JaredC01/LabStack/LabStack Modules/STLs/Module Radxa X4 with Heatsink/Module 1x Radxa X4 with Heatsink.stl

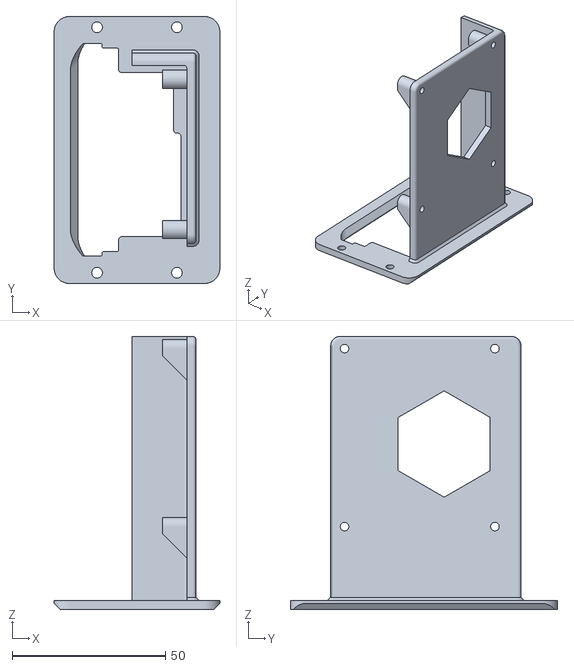
[picture p18: CAD file, 2025-01-17]
LabStack Modules/STLs/Module Radxa X4 with Heatsink/Module 1x Radxa X4 with Heatsink.stl
54.0 x 87.0 x 89.0
