JaredC01/LabStack/LabStack Mini/Accessories/STLs/M4 Mac Mini Spacer x2.stl

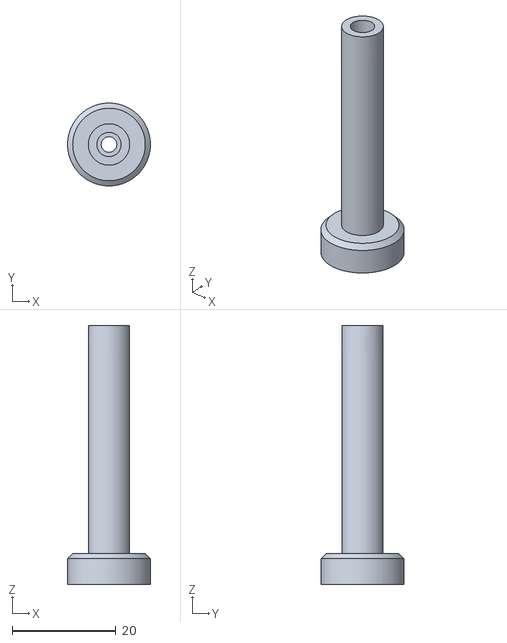
[picture p19: CAD file, 2025-01-20]
LabStack Mini/Accessories/STLs/M4 Mac Mini Spacer x2.stl
16.0 x 16.0 x 50.0
