JaredC01/LabStack/LabStack Modules/STLs/Module 2x Pi with Fan/Module 2x Pi with Fan.stl

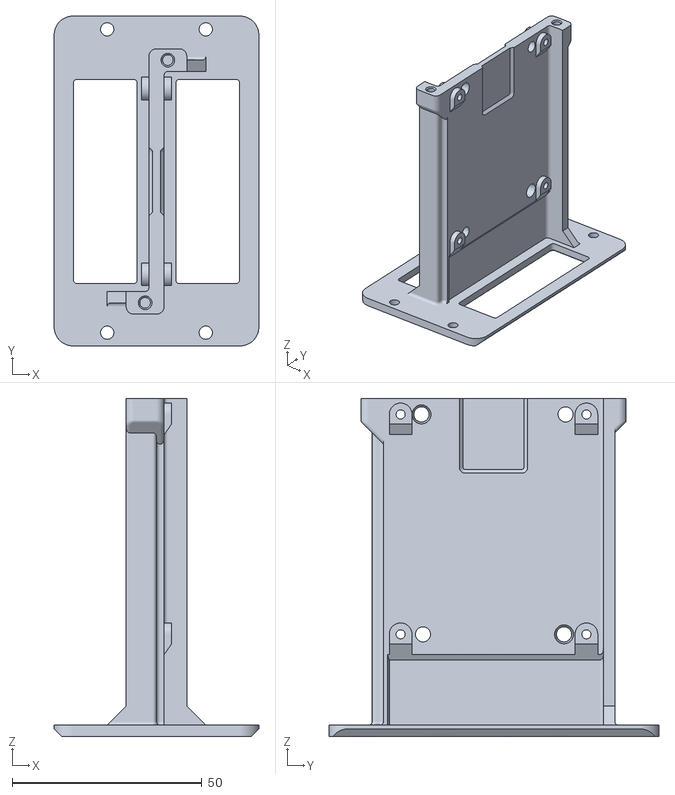
[picture p20: CAD file, 2025-08-05]
LabStack Modules/STLs/Module 2x Pi with Fan/Module 2x Pi with Fan.stl
54.0 x 87.0 x 89.1
