JaredC01/LabStack/LabStack Modules/STLs/Module 3x 25 SSD.stl

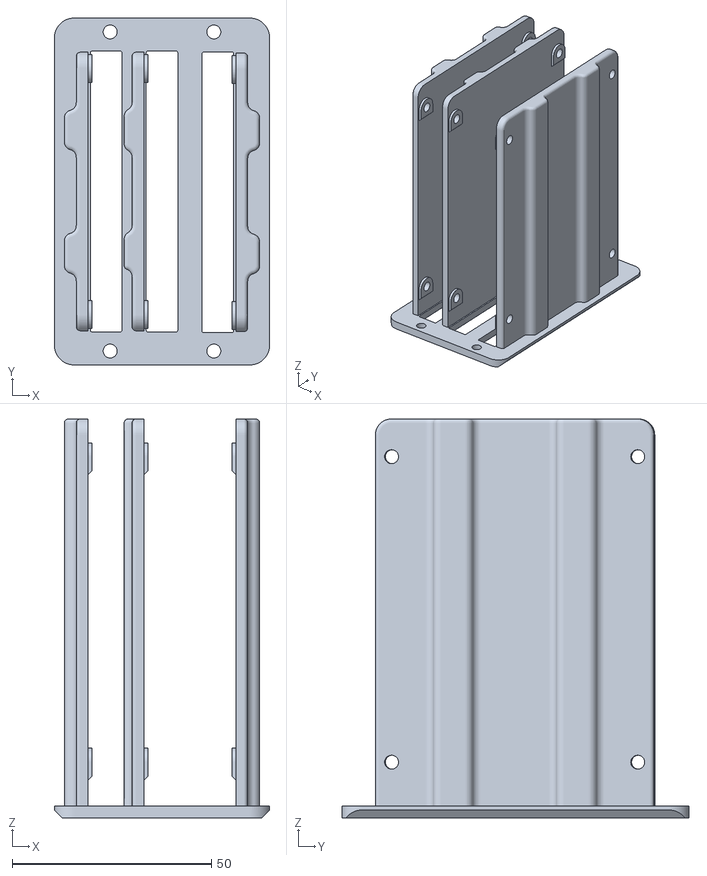
[picture p21: CAD file, 2025-02-13]
LabStack Modules/STLs/Module 3x 25 SSD.stl
54.0 x 87.0 x 100.0
