JaredC01/LabStack/LabStack Mini/Accessories/STLs/Split Bracket Brace x2.stl

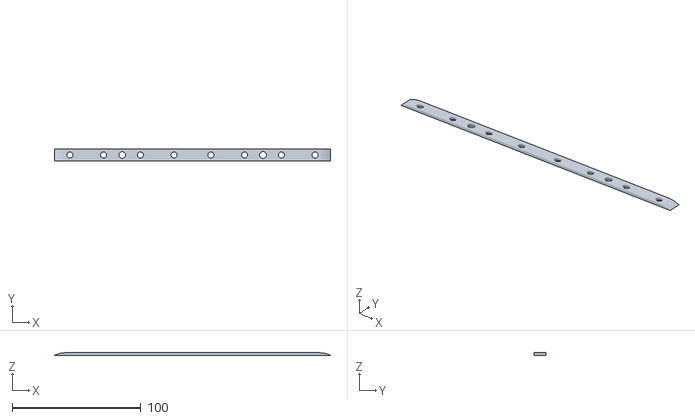
[picture p22: CAD file, 2025-01-18]
LabStack Mini/Accessories/STLs/Split Bracket Brace x2.stl
214.0 x 9.00 x 2.00
