JaredC01/LabStack/LabStack Modules/STLs/Module 1x Pi with 25 SSD.stl

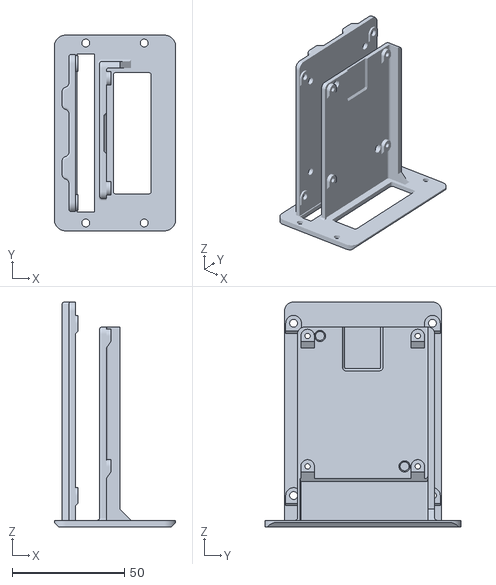
[picture p23: CAD file, 2025-02-13]
LabStack Modules/STLs/Module 1x Pi with 25 SSD.stl
54.0 x 87.0 x 100.0
