JaredC01/LabStack/LabStack Mini/Accessories/STLs/1U Mini 2x Keystone 2x SMA Left Mount.stl

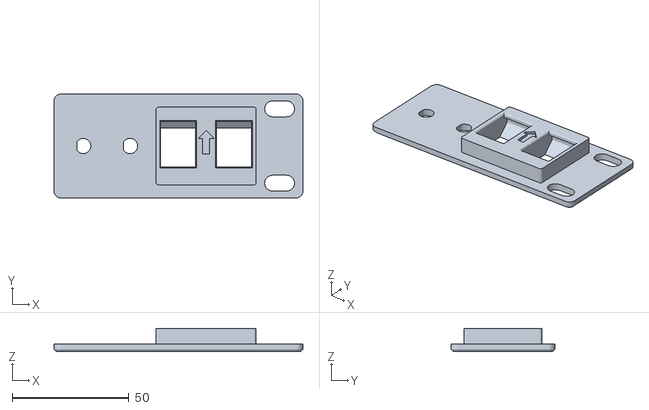
[picture p24: CAD file, 2025-01-17]
LabStack Mini/Accessories/STLs/1U Mini 2x Keystone 2x SMA Left Mount.stl
106.4 x 44.4 x 10.0
