JaredC01/LabStack/LabStack Modules/STLs/Module 2x 25 SSD.stl

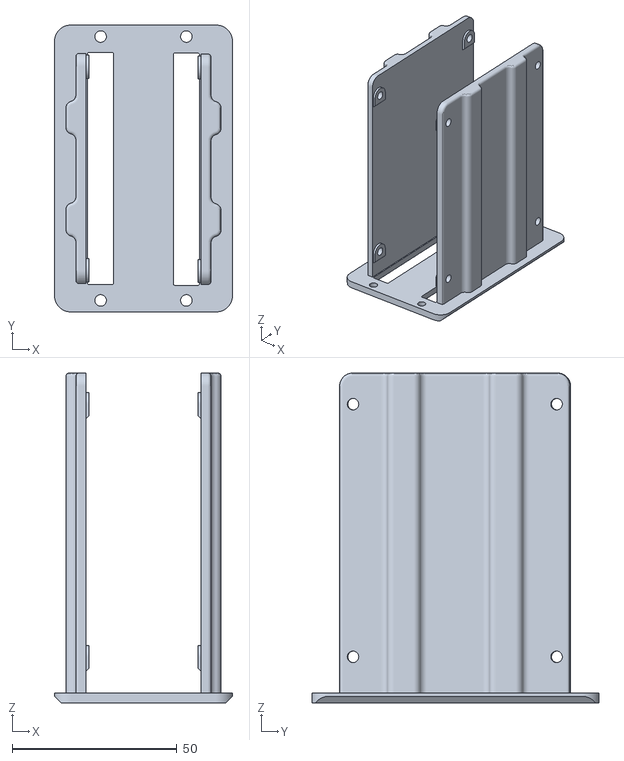
[picture p25: CAD file, 2025-02-12]
LabStack Modules/STLs/Module 2x 25 SSD.stl
54.0 x 87.0 x 100.0
