JaredC01/LabStack/LabStack Mini/Accessories/STLs/1U Mini 2x Keystone Right Mount.stl

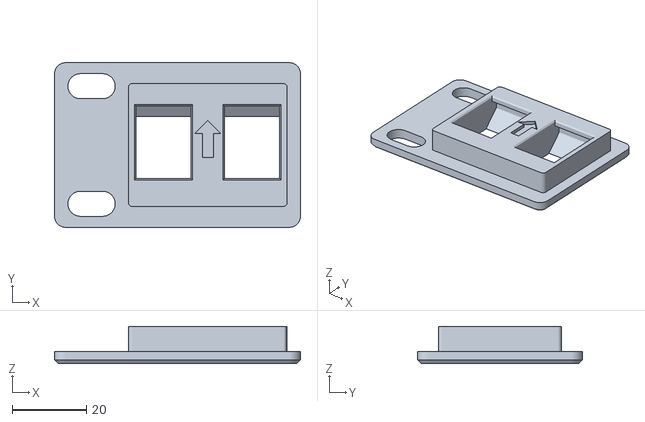
[picture p26: CAD file, 2025-01-17]
LabStack Mini/Accessories/STLs/1U Mini 2x Keystone Right Mount.stl
66.4 x 44.5 x 10.0
