JaredC01/LabStack/LabStack Modules/STLs/Module 1x JetKVM with Logo.stl

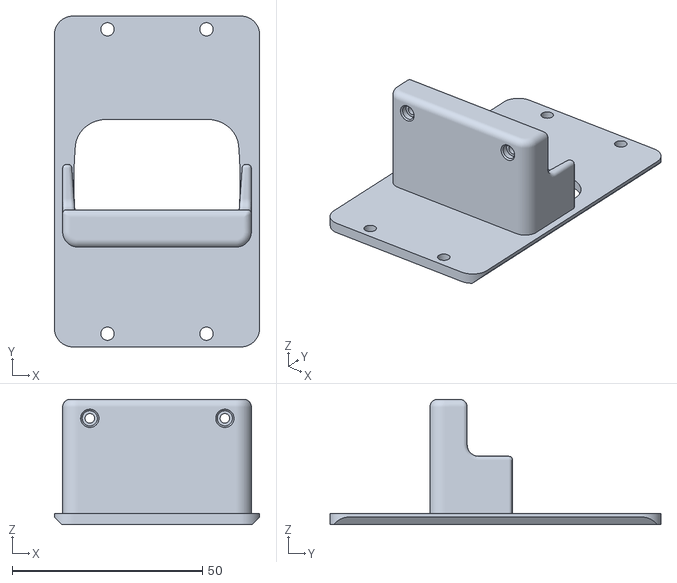
[picture p27: CAD file, 2025-02-12]
LabStack Modules/STLs/Module 1x JetKVM with Logo.stl
54.0 x 87.0 x 33.0
