JaredC01/LabStack/LabStack Modules/STLs/Module WaveShare 2.8in DSI Display.stl

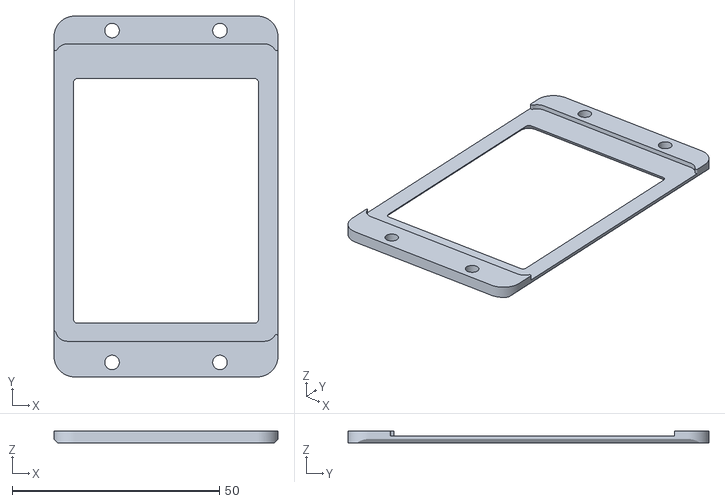
[picture p28: CAD file, 2025-01-31]
LabStack Modules/STLs/Module WaveShare 2.8in DSI Display.stl
54.0 x 87.0 x 3.00
