JaredC01/LabStack/LabStack Mini/Accessories/STLs/1U Mini Blank Panel.stl

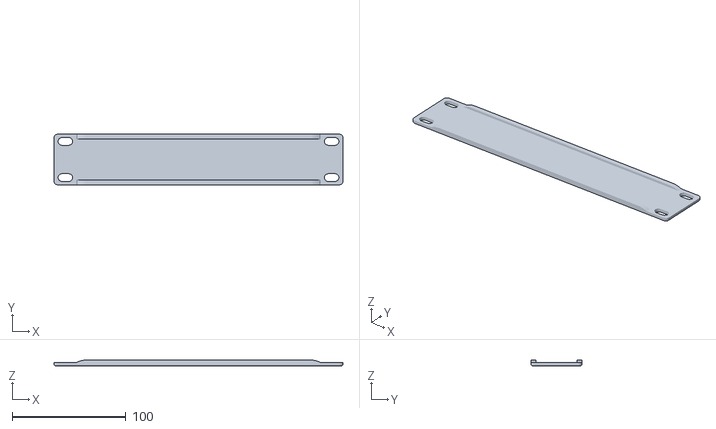
[picture p29: CAD file, 2025-01-17]
LabStack Mini/Accessories/STLs/1U Mini Blank Panel.stl
254.0 x 44.4 x 5.20
