JaredC01/LabStack/LabStack Mini/Accessories/STLs/2U Mini 2x 80mm Fan Panel.stl

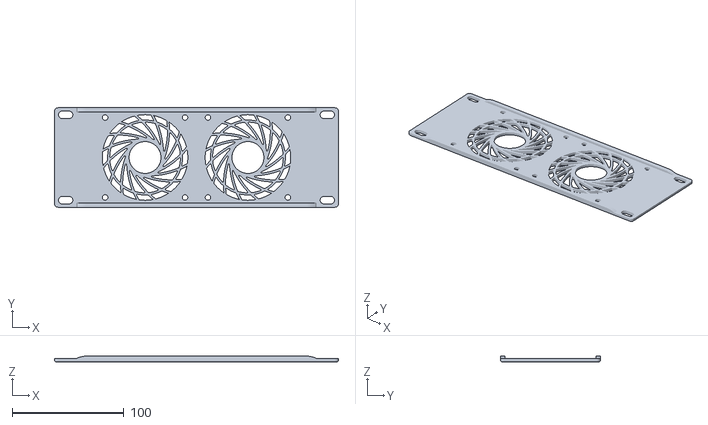
[picture p30: CAD file, 2025-01-17]
LabStack Mini/Accessories/STLs/2U Mini 2x 80mm Fan Panel.stl
254.0 x 89.0 x 5.20
