JaredC01/LabStack/LabStack Modules/STLs/Module 1x JetKVM 2x Keystone.stl

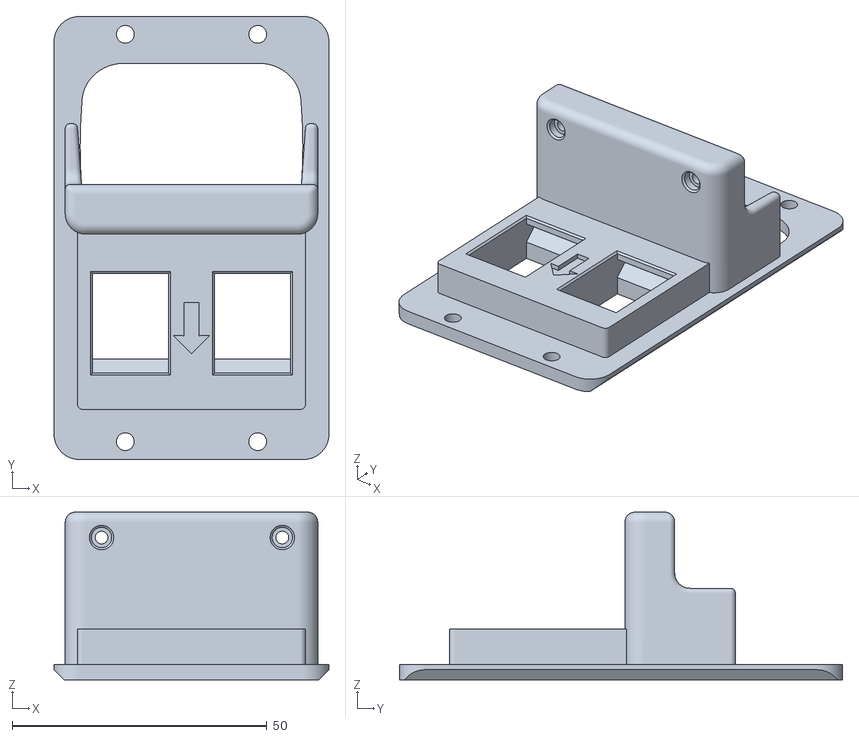
[picture p31: CAD file, 2025-01-20]
LabStack Modules/STLs/Module 1x JetKVM 2x Keystone.stl
54.0 x 87.0 x 33.0
