JaredC01/LabStack/LabStack Modules/STLs/Module 2x Keystone with Passthru.stl

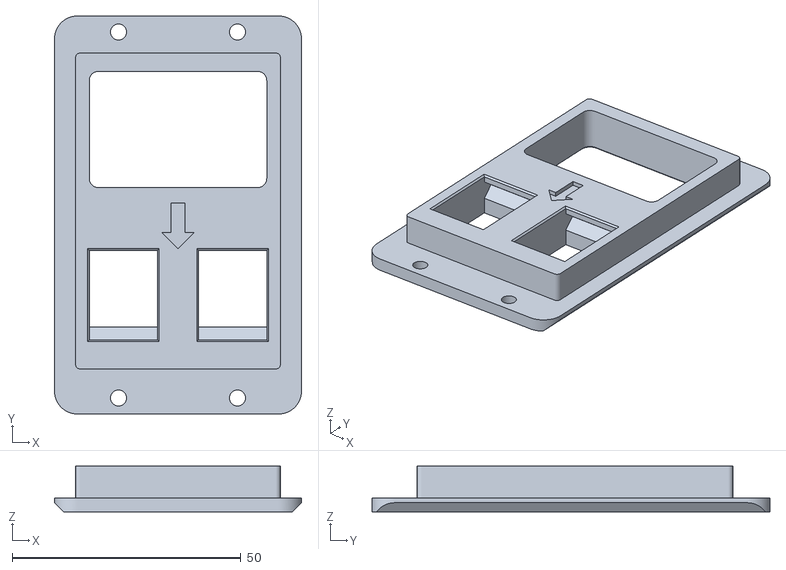
[picture p32: CAD file, 2025-01-17]
LabStack Modules/STLs/Module 2x Keystone with Passthru.stl
54.0 x 87.0 x 10.00
