JaredC01/LabStack/LabStack Modules/STLs/Module 4x Keystone.stl

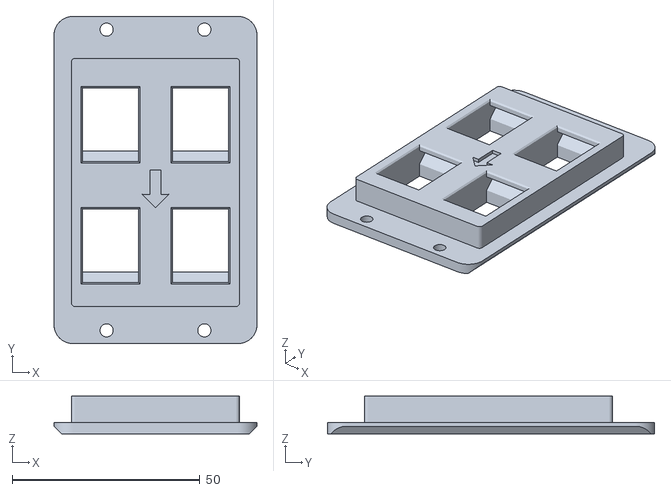
[picture p33: CAD file, 2025-01-17]
LabStack Modules/STLs/Module 4x Keystone.stl
54.0 x 87.0 x 10.0
