JaredC01/LabStack/LabStack Modules/STLs/Module Blank.stl

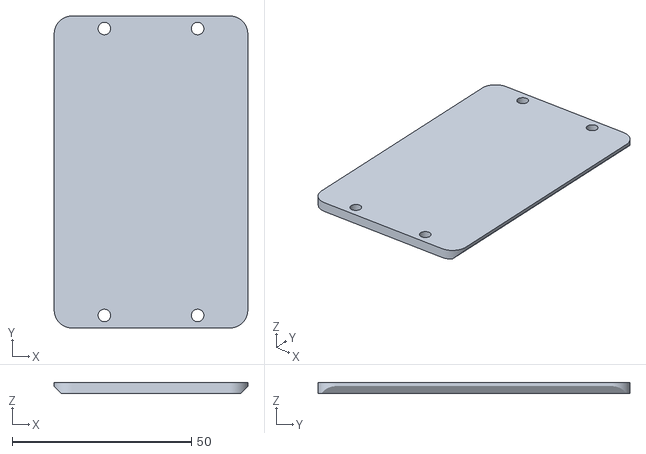
[picture p35: CAD file, 2025-01-17]
LabStack Modules/STLs/Module Blank.stl
54.0 x 87.0 x 3.00
