JaredC01/LabStack/LabStack Modules/STLs/Module 2x JetKVM.stl

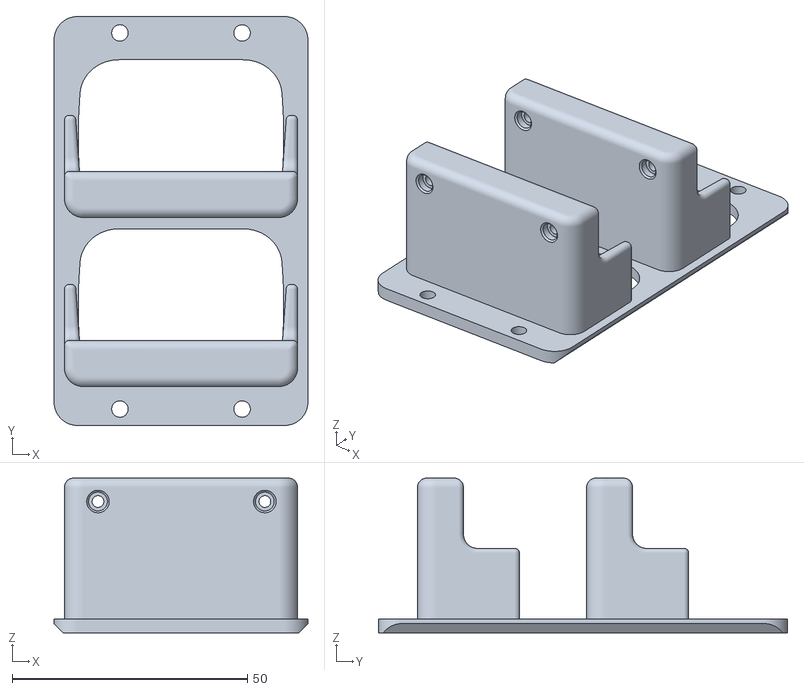
[picture p36: CAD file, 2025-01-17]
LabStack Modules/STLs/Module 2x JetKVM.stl
54.0 x 87.0 x 33.0
